tomaskovacik/HalogenDimmer/20210808_202836.jpg

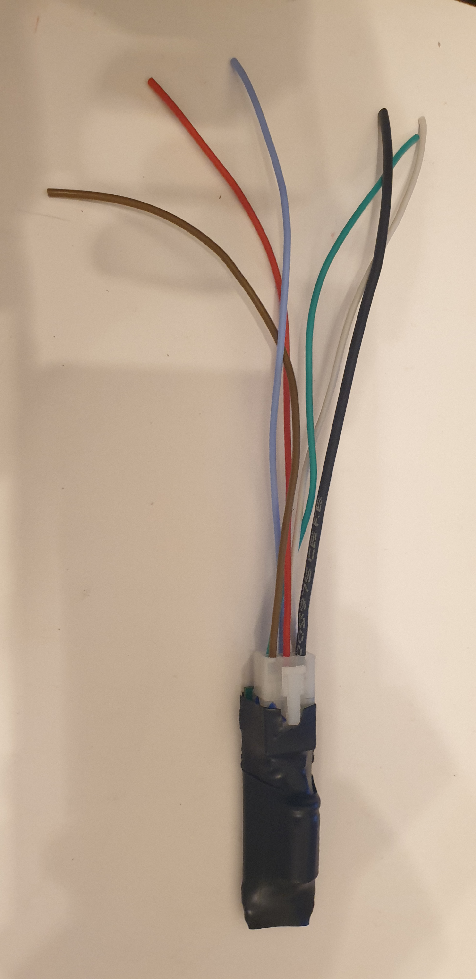
20210808_202836.jpg
